codemarv42/ExpressLRS/ELRS 2.4GHz TX/Mini ELRS 2.4GHz TX REV1/Mini ELRS 2.4GHz TX REV1 Render.PNG

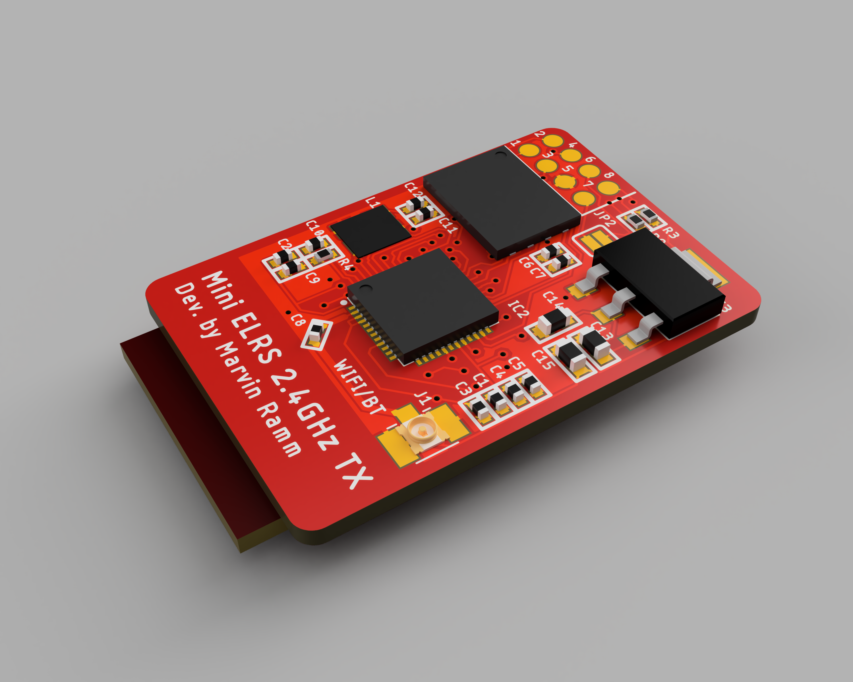
ELRS 2.4GHz TX/Mini ELRS 2.4GHz TX REV1/Mini ELRS 2.4GHz TX REV1 Render.PNG
